astuder/epc901/software/breakout/Core/Src/CmdExposure.cpp

/*
 * Shell command to configure exposure.
 *
 * Copyright 2020 by Adrian Studer
 *
 * Licensed under the terms of MIT License, all text here must be included in any redistribution.
 * See the LICENSE-SW file for details.
 */

#include "CmdExposure.hpp"
#include "Shell.hpp"
#include "Camera.hpp"
#include <cstring>

CmdExposure::CmdExposure(Camera* camera) {
	init("exposure",
		 "\texposure: Get current exposure time in microseconds.\r\n"
		 "\texposure max: Get maximum exposure time supported.\r\n"
		 "\texposure <time>: Set exposure time in microseconds.\r\n");
	_camera = camera;
}

void CmdExposure::handler(Shell* shell) {
	if (!shell) {
		return;
	}

	if (!_camera) {
		shell->error("No camera!");
		return;
	}

	const char* param = shell->readParam();
	if (!param) {
		shell->writeInt(_camera->getExposureTime());
		shell->newline();
		return;
	}

	if (0 == stricmp(param, "max")) {
		shell->writeInt(_camera->getMaxExposureTime());
		shell->newline();
		return;
	}

	uint32_t time_us = shell->paramToUInt(param);
	if (0 == time_us || 0 == stricmp("auto", param)) {
		// TODO: Auto exposure
		shell->error("Auto exposure not implemented yet.");
		return;
	}

	if (time_us > _camera->getMaxExposureTime()) {
		shell->error("Exposure exceed maximum exposure time supported.");
		return;
	}

	_camera->setExposureTime(time_us);
	shell->ok();
}
