astuder/epc901/software/python/camera.py

# Test application for EPC901 breakout board

import serial
import sys
import argparse
from textwrap import wrap
import matplotlib.pyplot as plt
import matplotlib.animation as animation

class Camera:    
    ser = serial.Serial()
    def open(self, port, speed=115200):
        try:
            self.ser = serial.Serial(port, speed, timeout=1)
            self.ser.write(b"@echo off\n")
            self.ser.readline()
            self.ser.readline()
        except Exception as e:
            print("Failed to connect to sensor on port ", port)
            print("Exception: " + str(e))
            sys.exit()

    def close(self):
        self.ser.write(b"@echo on\n")
        self.ser.readline()
        self.ser.close()

    def setExposure(self, exposure):
        exposure_str = "@exposure {}\n".format(exposure).encode("utf-8");
        self.ser.write(exposure_str)
        self.ser.readline()     # ok

    def capture(self):
        self.ser.write(b"@capture\n")
        self.ser.readline()     # ok

    def getPixels(self):
        self.ser.write(b"@transfer\n")
        frame_meta = self.ser.readline()     # frame number, timestamp, exposure
        frame_data = [int(x, 16) for x in wrap(self.ser.readline().decode("utf-8"), 4)]
        return frame_data

camera = Camera()

def loop(i):
    camera.capture() 
    yar = camera.getPixels()
    # print(yar)
    ax1.clear()
    ax1.set_ylim((0, 3000), auto=False)
    ax1.plot(yar)

# read command line arguments
# we expect camera.py -p <serial port> -e <exposure time in ms>
parser = argparse.ArgumentParser(description="EPC901 camera 0.1")
parser.add_argument("-p", help="serial port of camera, for example /dev/serial0 or COM3", dest="port", required=True)
parser.add_argument("-e", help="exposure time in milliseconds", dest="exposure", default=1000)
args = parser.parse_args()

camera.open(args.port)
camera.setExposure(args.exposure)

fig = plt.figure()
ax1 = fig.add_subplot(1,1,1)

ani = animation.FuncAnimation(fig, loop, interval=100)
plt.show()
camera.close()
